Ozonised/TPFR_Meter/Schematic/Kicad/TPFR_Meter.kicad_sch

## KiCad design Schematic/Kicad/TPFR_Meter.kicad_sch (2023-05-14)

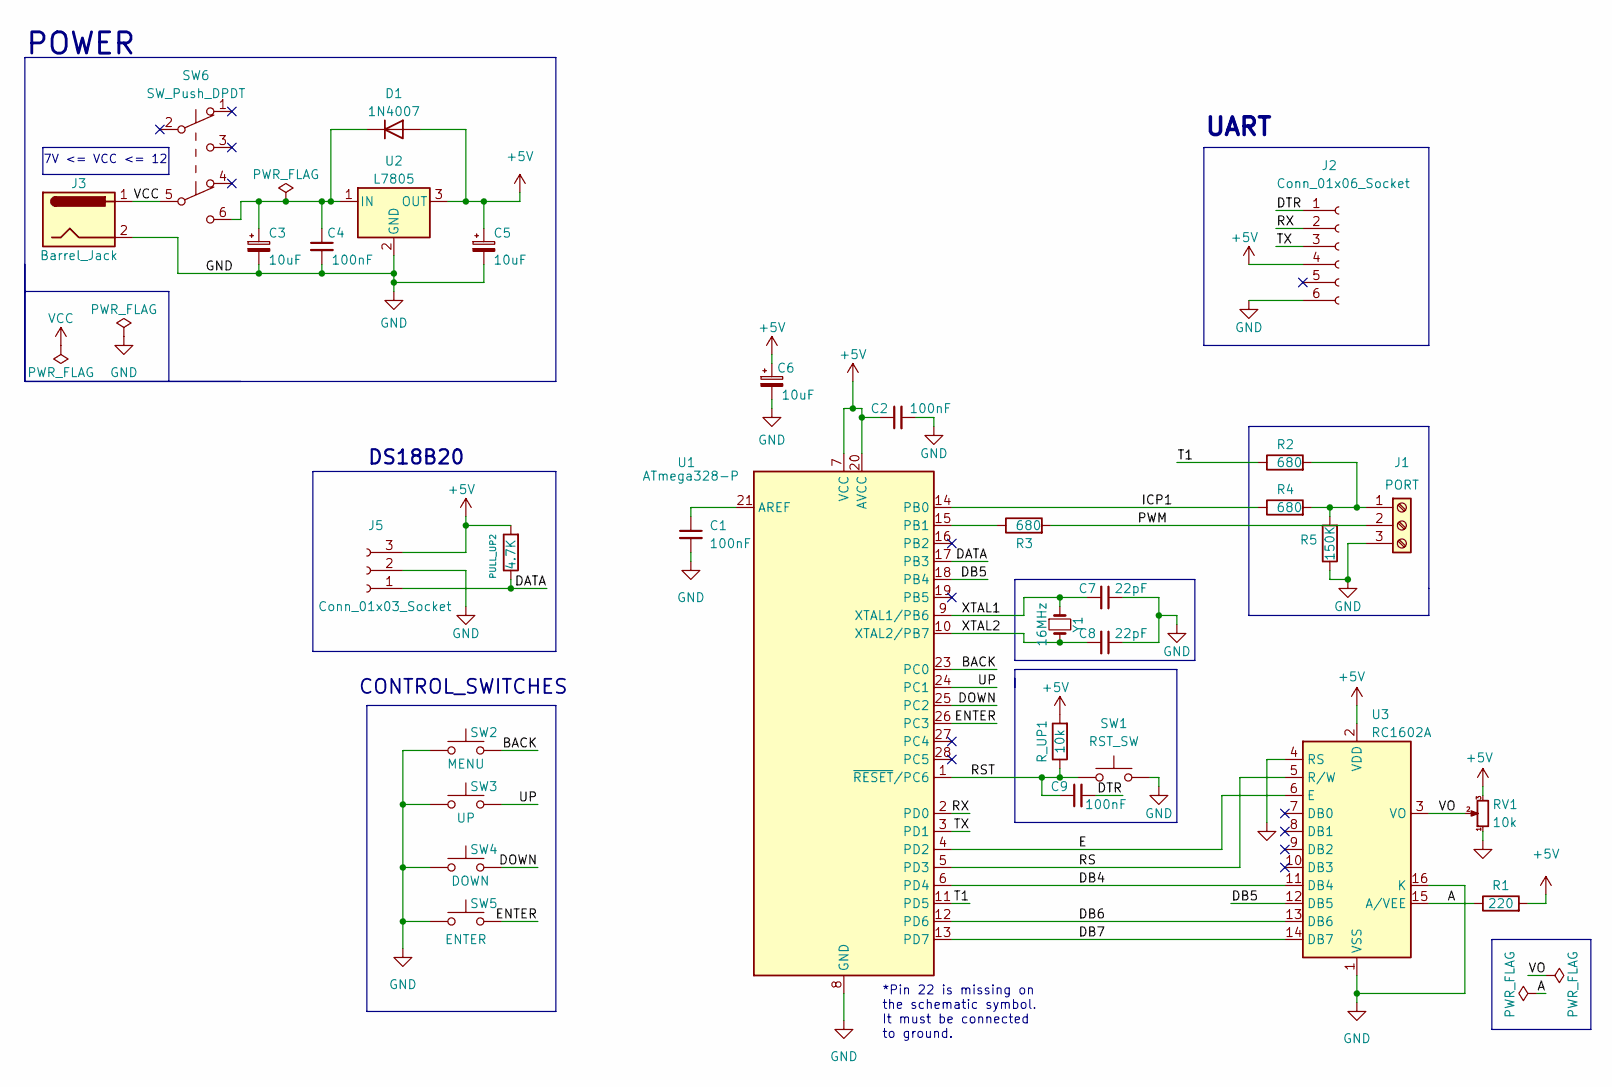
[picture p19: schematic TPFR_Meter.kicad_sch]

Parts:
C1, C2, C4, C9: 100nF; C_Disc_D5.0mm_W2.5mm_P2.50mm
C3, C5, C6: 10uF; CP_Radial_D5.0mm_P2.50mm
C7, C8: 22pF; C_Disc_D5.0mm_W2.5mm_P2.50mm
D1: 1N4007; D_DO-41_SOD81_P10.16mm_Horizontal
J1: PORT; TerminalBlock_Altech_AK300-3_P5.00mm
J2: Conn_01x06_Socket; PinSocket_1x06_P2.54mm_Horizontal
J3: Barrel_Jack; BarrelJack_Horizontal
J5: Conn_01x03_Socket; PinSocket_1x03_P2.54mm_Vertical
PULL_UP2: 4.7K; R_Axial_DIN0207_L6.3mm_D2.5mm_P7.62mm_Horizontal
R1: 220; R_Axial_DIN0207_L6.3mm_D2.5mm_P7.62mm_Horizontal
R2, R3, R4: 680; R_Axial_DIN0207_L6.3mm_D2.5mm_P7.62mm_Horizontal
R5: 150K; R_Axial_DIN0207_L6.3mm_D2.5mm_P7.62mm_Horizontal
RV1: 10k; Potentiometer_Runtron_RM-065_Vertical
R_UP1: 10k; R_Axial_DIN0207_L6.3mm_D2.5mm_P7.62mm_Horizontal
SW1: RST_SW; SW_PUSH_6mm_H4.3mm
SW2: MENU; SW_PUSH_6mm_H4.3mm
SW3: UP; SW_PUSH_6mm_H4.3mm
SW4: DOWN; SW_PUSH_6mm_H4.3mm
SW5: ENTER; SW_PUSH_6mm_H4.3mm
SW6: SW_Push_DPDT; SW_Push_2P2T_Toggle_CK_PVA2xxH1xxxxxxV2
U1: ATmega328-P; DIP-28_W7.62mm
U2: L7805; TO-220-3_Horizontal_TabDown
U3: RC1602A; LCD-1602A
Y1: 16MHz; Crystal_HC49-4H_Vertical

Connections:
+5V: C2.1, C5.1, C6.1, D1.2 (A), J2.4, J5.3, PULL_UP2.2, R1.2, RV1.3, R_UP1.2, U1.7 (VCC), U1.20 (AVCC), U2.3 (OUT), U3.2 (VDD)
A: R1.1, U3.15 (A/VEE)
BACK: SW2.2, U1.23 (PC0)
DATA: J5.1, PULL_UP2.1, U1.17 (PB3)
DB4: U1.6 (PD4), U3.11 (DB4)
DB5: U1.18 (PB4), U3.12 (DB5)
DB6: U1.12 (PD6), U3.13 (DB6)
DB7: U1.13 (PD7), U3.14 (DB7)
DOWN: SW4.2, U1.25 (PC2)
DTR: C9.2, J2.1
E: U1.4 (PD2), U3.6 (E)
ENTER: SW5.2, U1.26 (PC3)
GND: C1.2, C2.2, C3.2, C4.2, C5.2, C6.2, C7.1, C8.1, J1.3, J2.6, J3.2, J5.2, R5.1, RV1.1, SW1.2, SW2.1, SW3.1, SW4.1, SW5.1, U1.8 (GND), U1.22 (GND), U2.2 (GND), U3.1 (VSS), U3.4 (RS), U3.16 (K)
ICP1: R4.1, U1.14 (PB0)
unnamed: C1.1, U1.21 (AREF)
unnamed: C3.1, C4.1, D1.1 (K), SW6.6 (C), U2.1 (IN)
unnamed: J1.1, R2.2, R4.2, R5.2
unnamed: R3.1, U1.15 (PB1)
PWM: J1.2, R3.2
RS: U1.5 (PD3), U3.5 (R/W)
RST: C9.1, R_UP1.1, SW1.1, U1.1 (~RESET/PC6)
RX: J2.2, U1.2 (PD0)
T1: R2.1, U1.11 (PD5)
TX: J2.3, U1.3 (PD1)
UP: SW3.2, U1.24 (PC1)
VCC: J3.1, SW6.5 (B)
VO: RV1.2, U3.3 (VO)
XTAL1: C7.2, U1.9 (XTAL1/PB6), Y1.1
XTAL2: C8.2, U1.10 (XTAL2/PB7), Y1.2

Notes on the sheet:
DS18B20
*Pin 22 is missing on the schematic symbol. It must be connected to ground.
UART
POWER
7V <= VCC <= 12
CONTROL_SWITCHES
