Ozonised/TPFR_Meter/TPFR_Meter_Firmware/include/pwm.h

#pragma once

#include "common.h"

/// @brief Minimun and maximum PWM frequency in the selected range
struct PWM_Freq_Range
{
    const uint32_t MIN_FREQ;
    const uint32_t MAX_FREQ;
    const uint16_t STEP;
};

#define PWM_PIN PB1

#define R0 0
#define R1 1
#define R2 2
#define R3 3

void PWM_Range_Select();
